analoghifi/Transformer-Snubber/hardware/THT/Quasimodo_V4_TH_sch.png

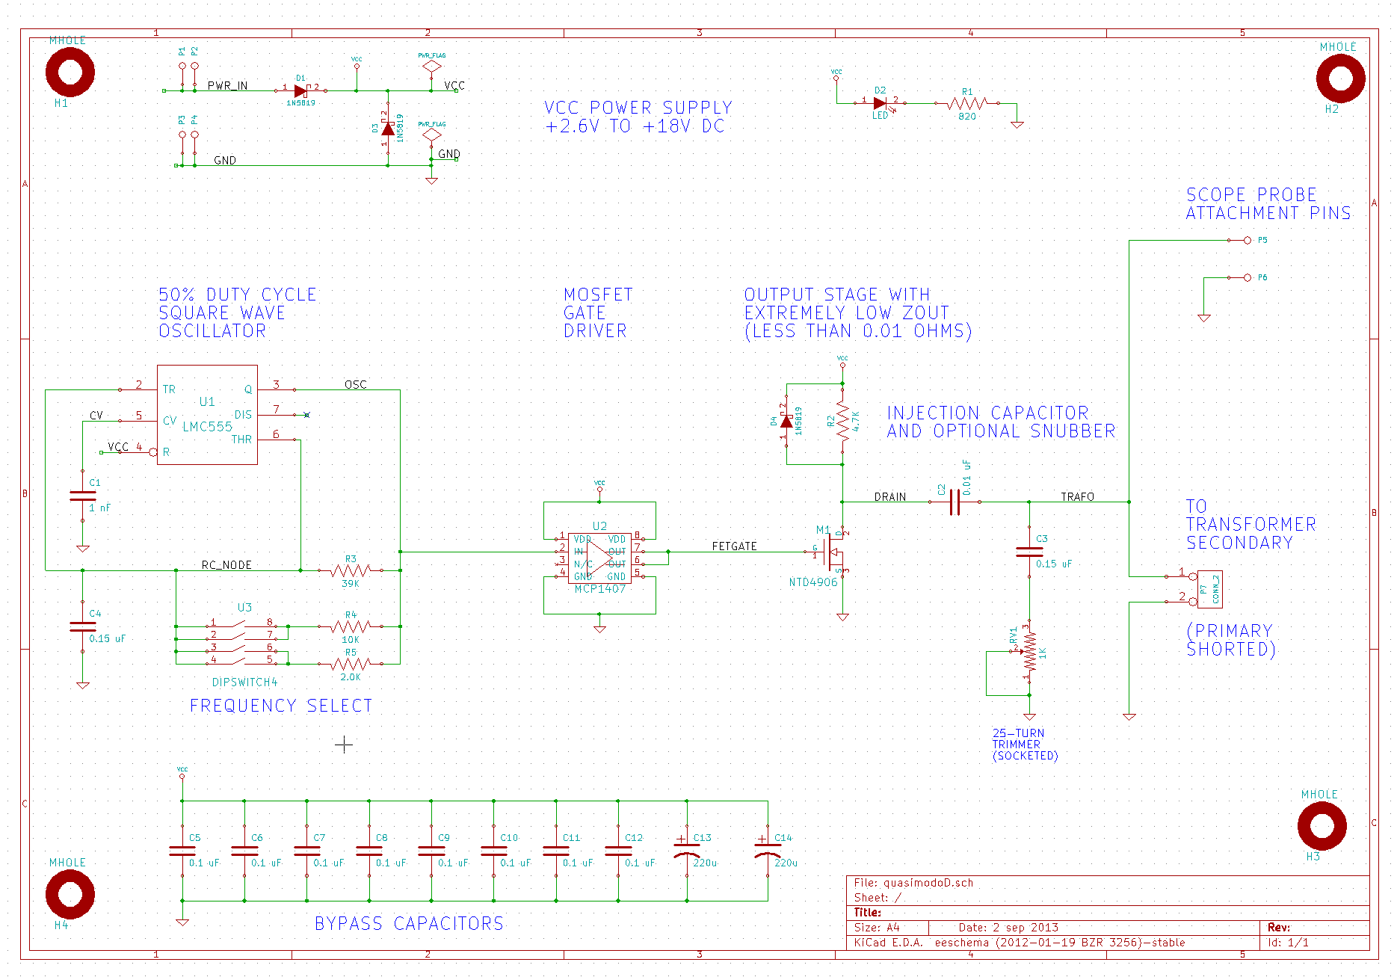
hardware/THT/Quasimodo_V4_TH_sch.png
